jan-baranowski/atx-form-card/doc/blogpost/img/1 (3).png

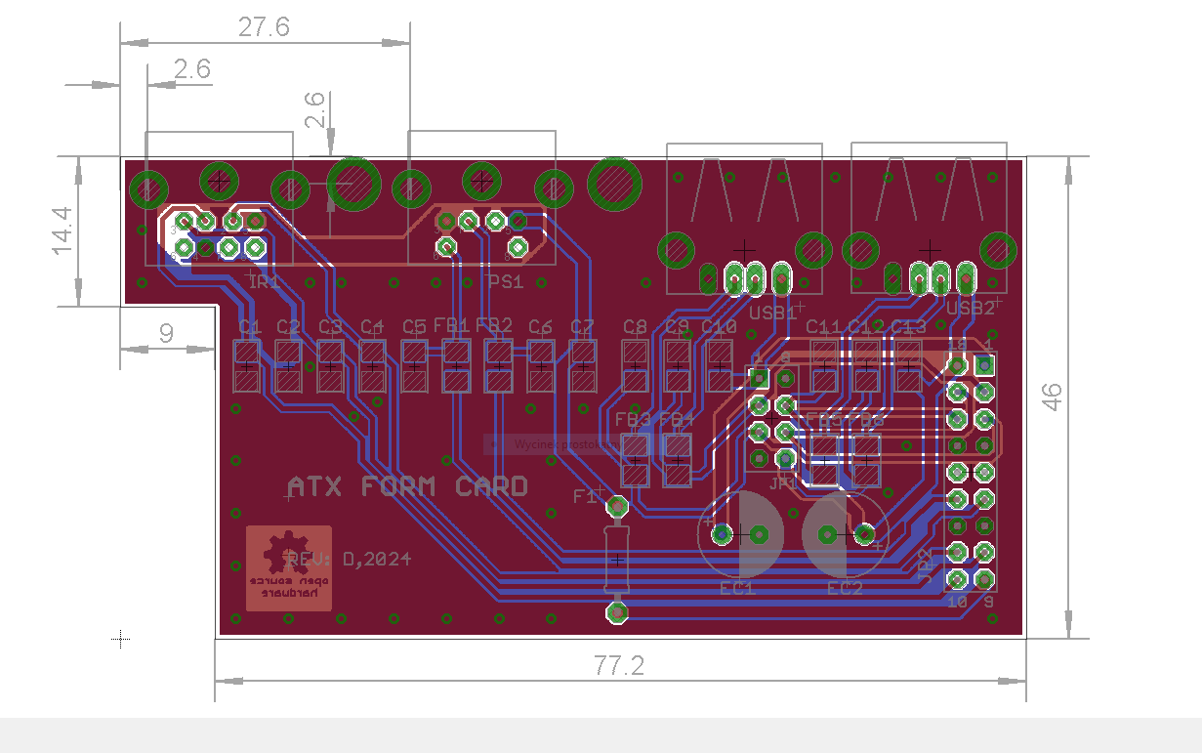
doc/blogpost/img/1 (3).png
