jan-baranowski/atx-form-card/doc/blogpost/img/1.png

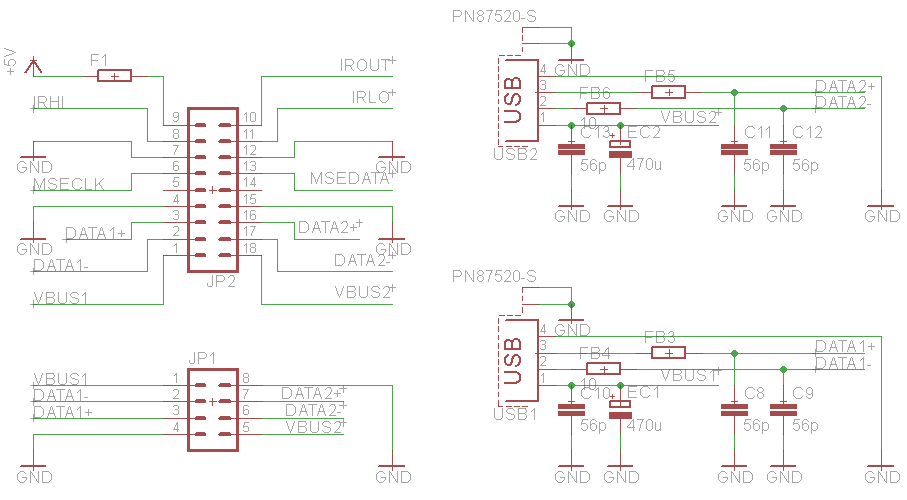
doc/blogpost/img/1.png
