jan-baranowski/atx-form-card/doc/blogpost/img/2 (2).PNG

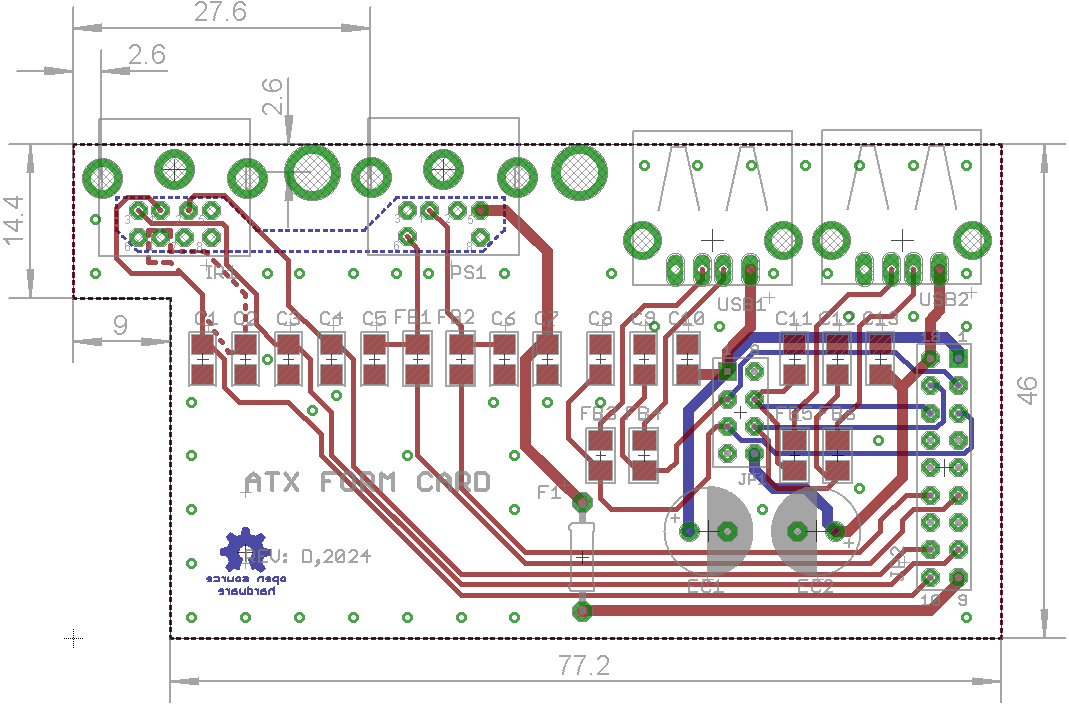
doc/blogpost/img/2 (2).PNG
