jan-baranowski/atx-form-card/doc/blogpost/img/2 (3).PNG

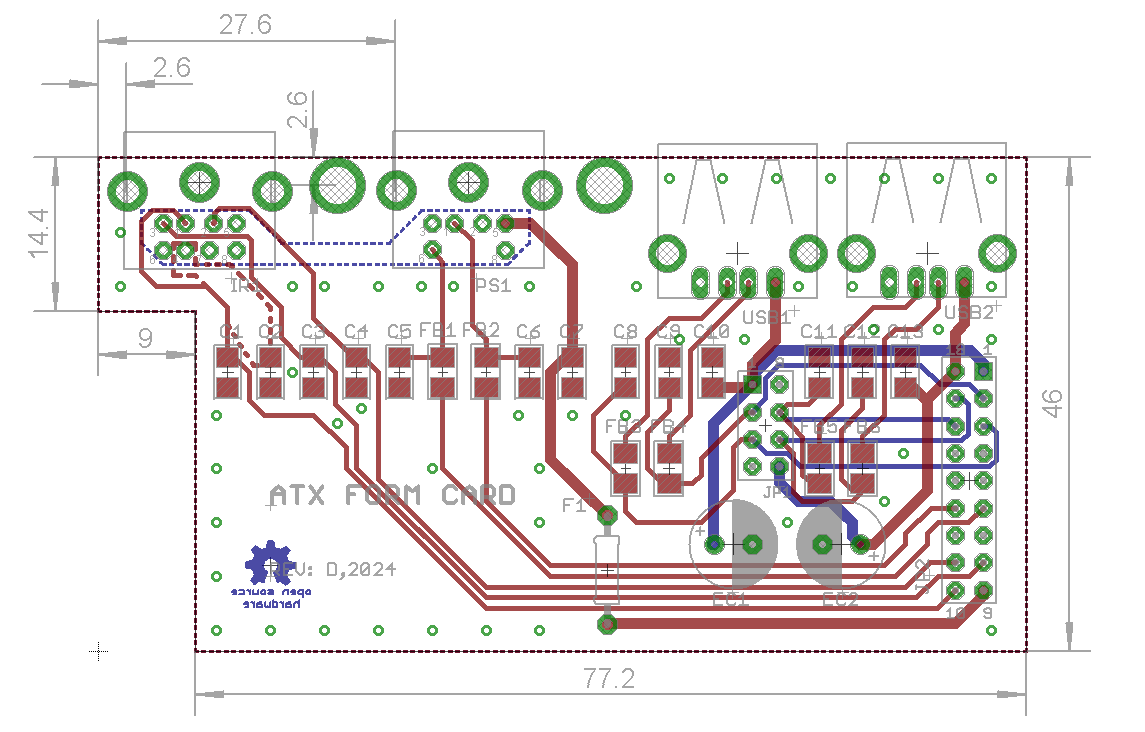
doc/blogpost/img/2 (3).PNG
