jan-baranowski/atx-form-card/doc/blogpost/img/2.png

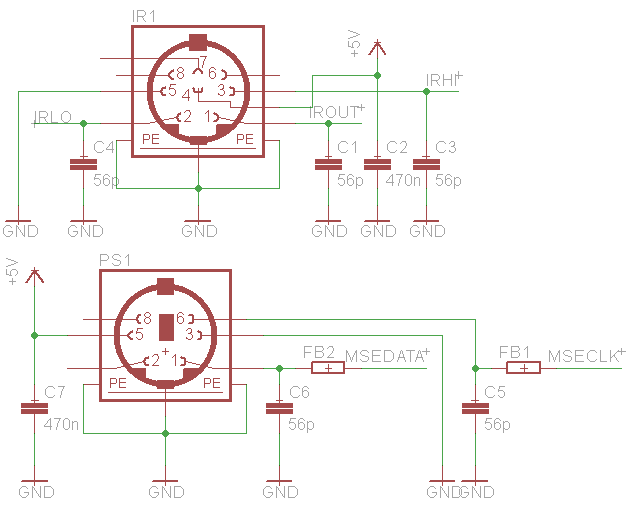
doc/blogpost/img/2.png
