jan-baranowski/atx-form-card/doc/blogpost/img/40dda3264b389b13b18e15fa20d9.jpg

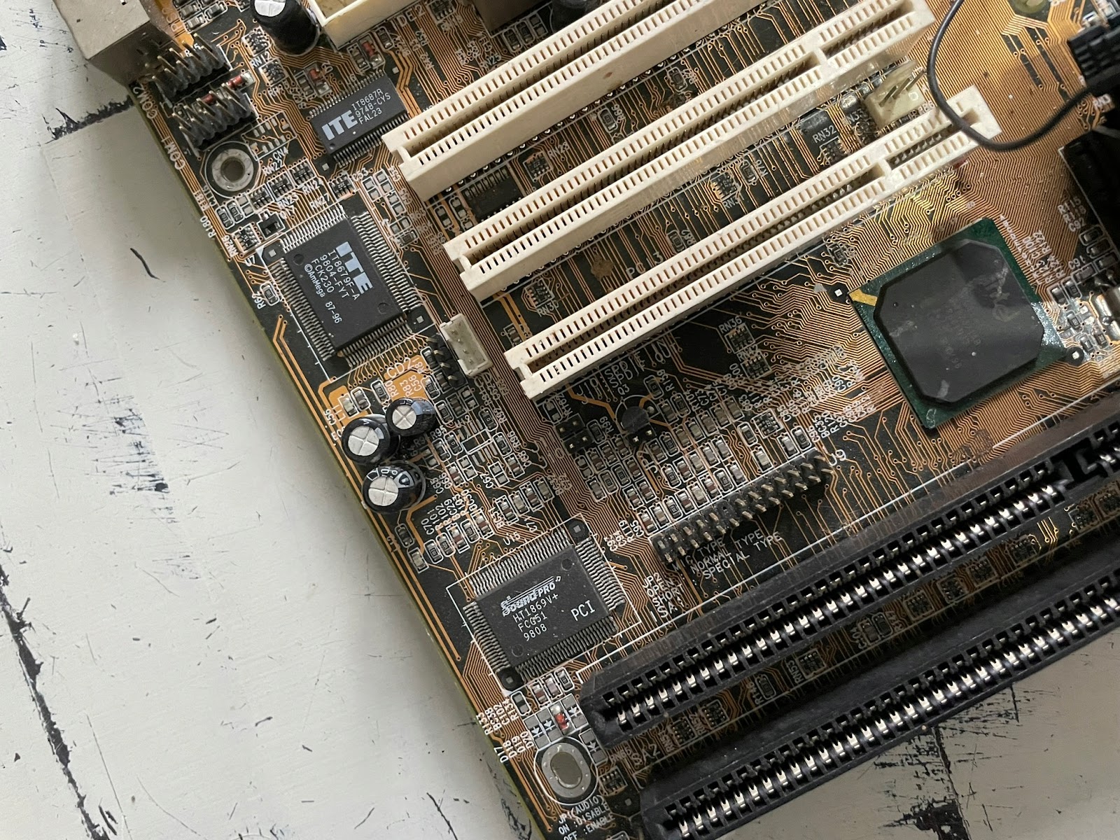
doc/blogpost/img/40dda3264b389b13b18e15fa20d9.jpg
