jan-baranowski/atx-form-card/doc/blogpost/img/2350c0874c018ecbfe8285fe1adc.jpg

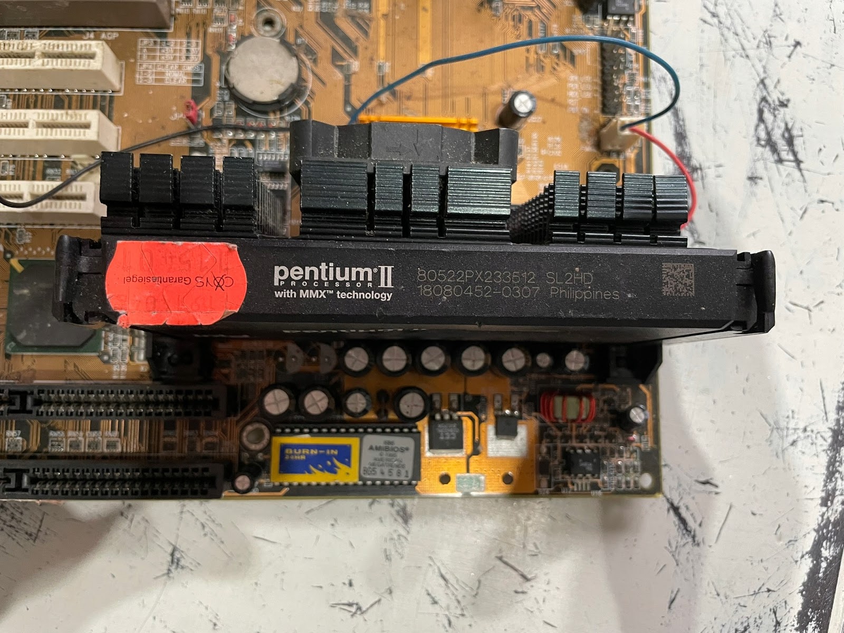
doc/blogpost/img/2350c0874c018ecbfe8285fe1adc.jpg
