jan-baranowski/atx-form-card/doc/blogpost/img/127271-002jpg_cf48e4d2-c9a6-482c-9bfb-930e1088c480_1024x1024.jpg

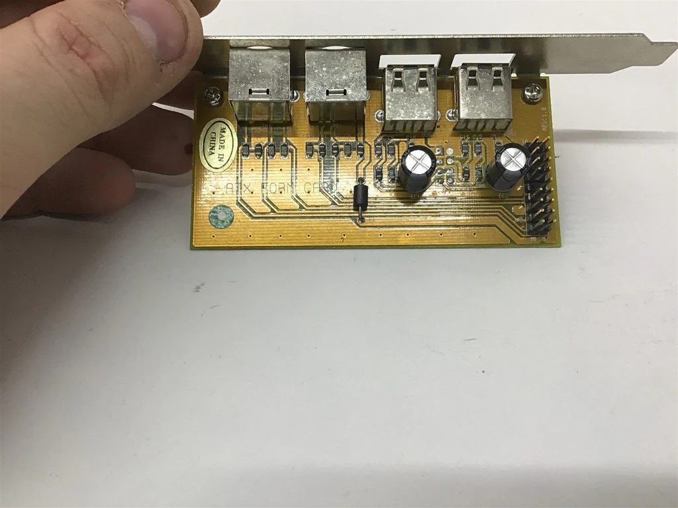
doc/blogpost/img/127271-002jpg_cf48e4d2-c9a6-482c-9bfb-930e1088c480_1024x1024.jpg
