jan-baranowski/atx-form-card/doc/blogpost/img/127271-004jpg_7a8d4e18-62b3-4fa2-aa82-eddd27a5ec42_1024x1024.jpg

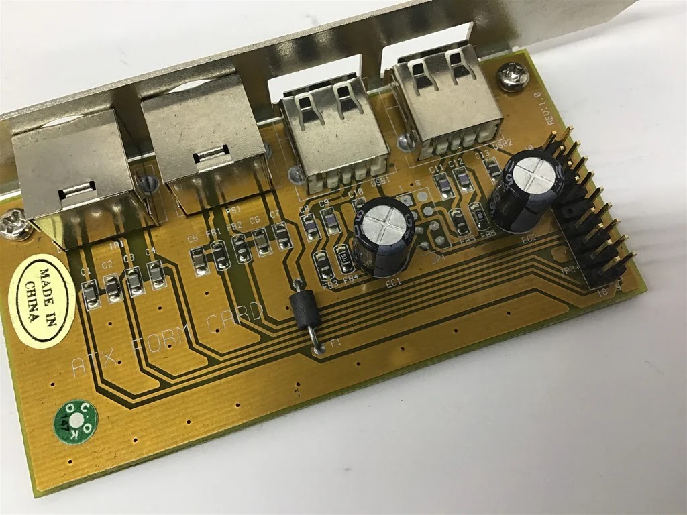
doc/blogpost/img/127271-004jpg_7a8d4e18-62b3-4fa2-aa82-eddd27a5ec42_1024x1024.jpg
