jan-baranowski/atx-form-card/doc/blogpost/img/127271-005jpg_ed1939dc-fdf4-4473-9c96-21b9dd0ac8c7_1024x1024.jpg

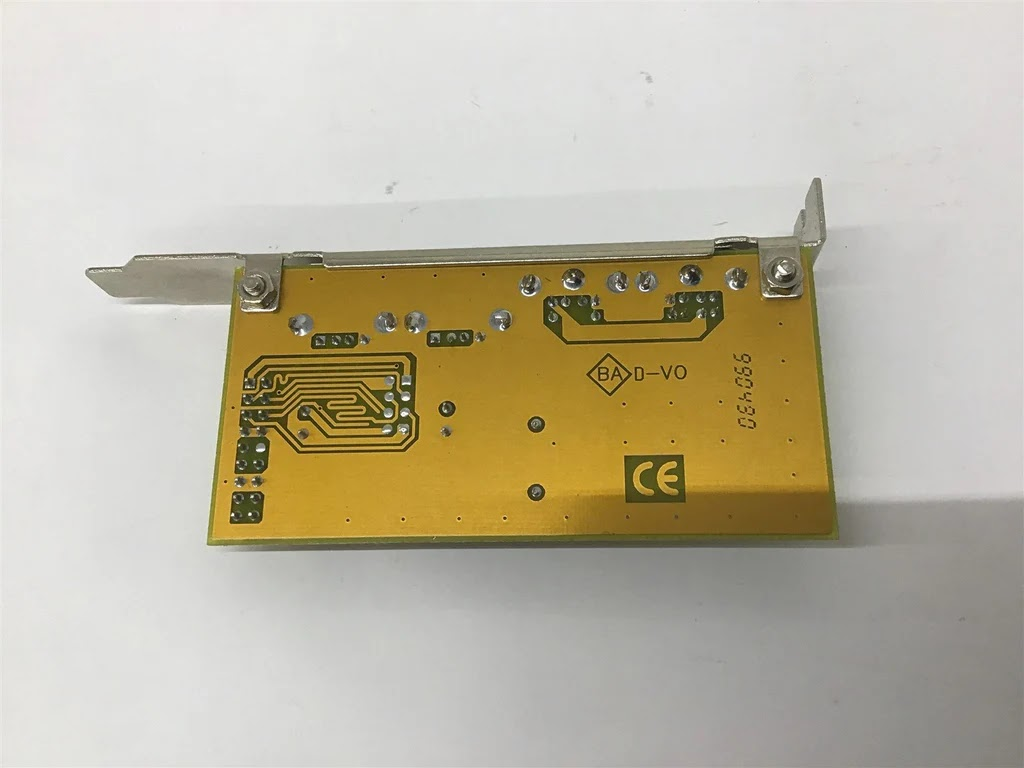
doc/blogpost/img/127271-005jpg_ed1939dc-fdf4-4473-9c96-21b9dd0ac8c7_1024x1024.jpg
