jan-baranowski/atx-form-card/doc/blogpost/img/288669ee4a689a44cc89ebede7dc.jpg

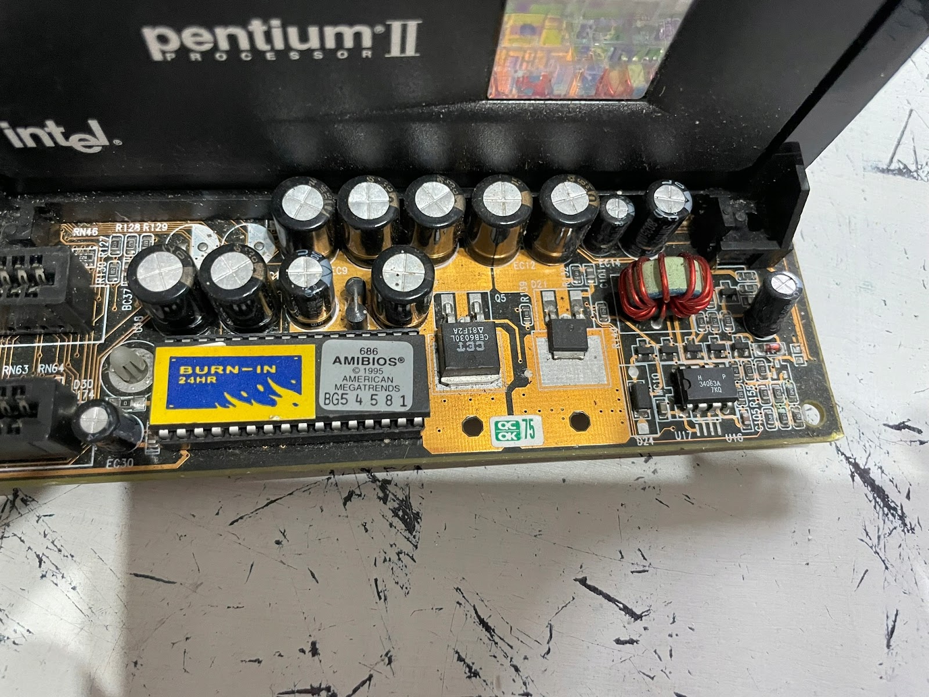
doc/blogpost/img/288669ee4a689a44cc89ebede7dc.jpg
