jan-baranowski/atx-form-card/doc/blogpost/img/atx-form-card.jpg

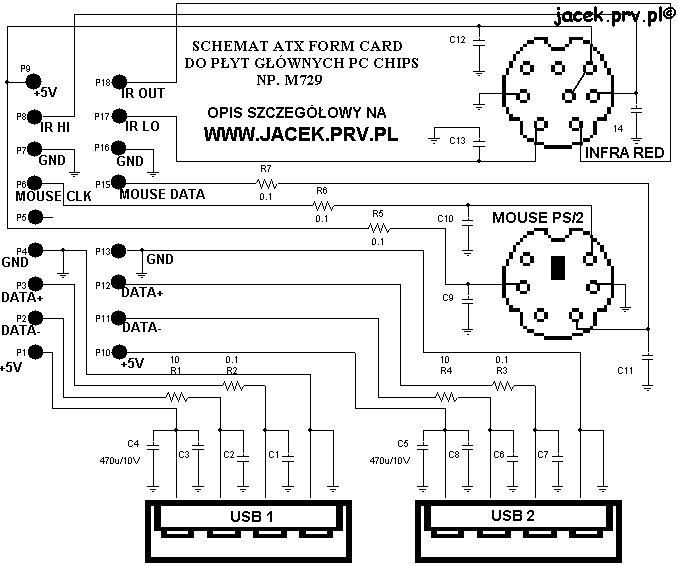
doc/blogpost/img/atx-form-card.jpg
