jan-baranowski/atx-form-card/doc/blogpost/img/bf811de64155b05a6d7ccc6c4f51.jpg

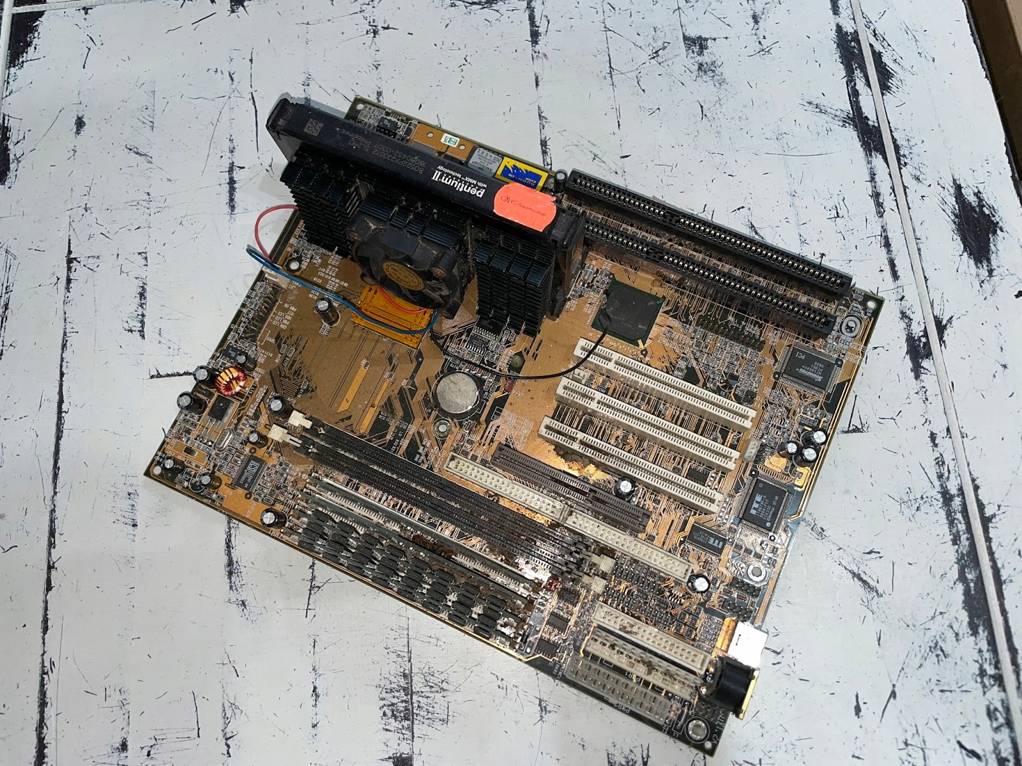
doc/blogpost/img/bf811de64155b05a6d7ccc6c4f51.jpg
