jan-baranowski/atx-form-card/doc/blogpost/img/efacdf3442a0b99acd3ed1cdcaee.jpg

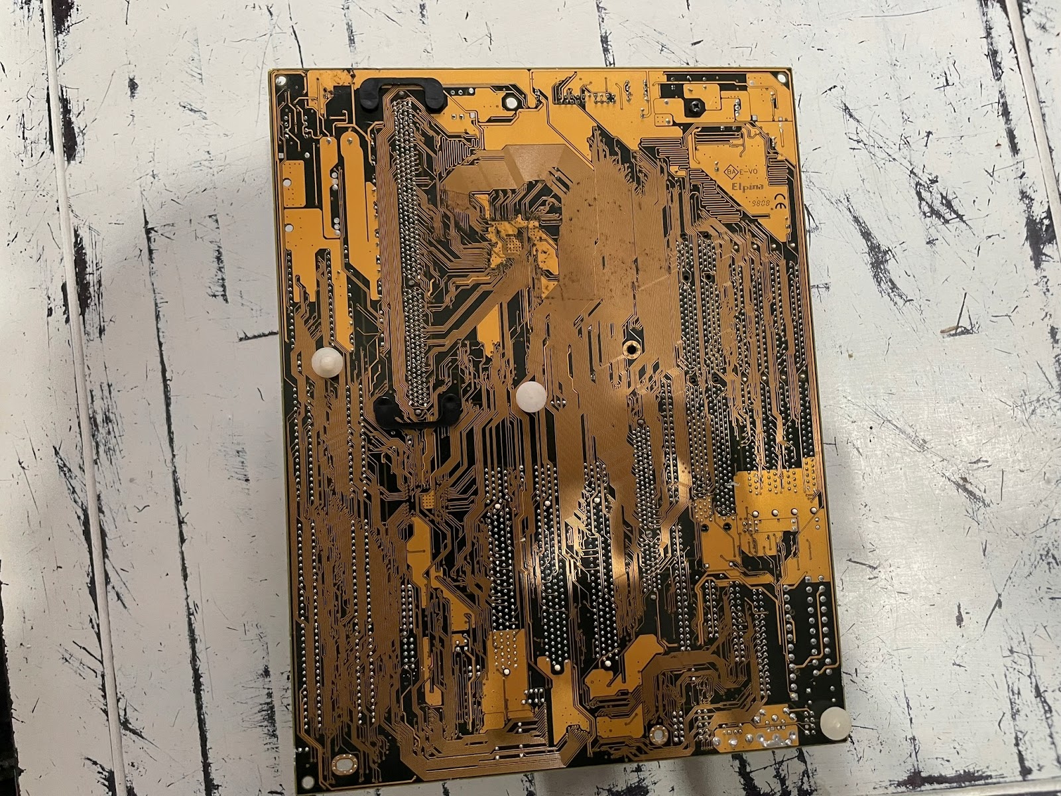
doc/blogpost/img/efacdf3442a0b99acd3ed1cdcaee.jpg
