jan-baranowski/atx-form-card/doc/blogpost/img/image;s=360x0.jpg

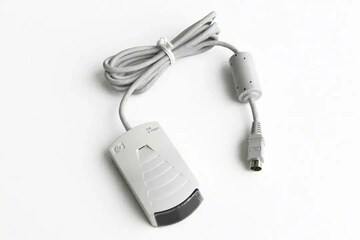
doc/blogpost/img/image;s=360x0.jpg
