jan-baranowski/atx-form-card/doc/blogpost/img/IMG_20240930_183724.jpg

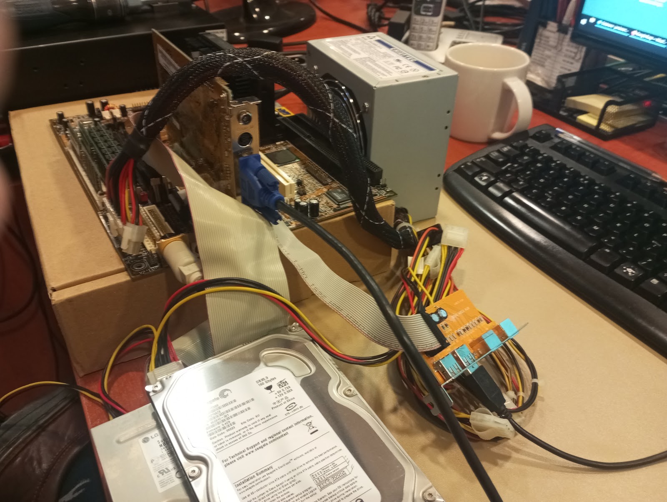
doc/blogpost/img/IMG_20240930_183724.jpg
