jan-baranowski/atx-form-card/doc/blogpost/img/IMG_20241005_171047_done_pciisa.jpg

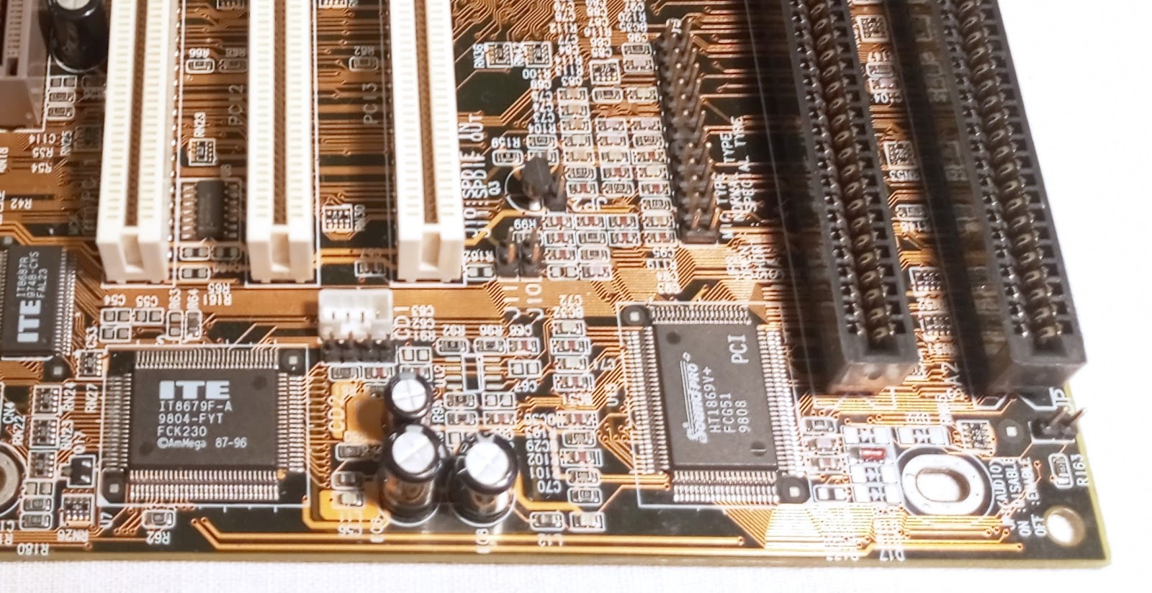
doc/blogpost/img/IMG_20241005_171047_done_pciisa.jpg
