jan-baranowski/atx-form-card/doc/blogpost/img/IMG_20241009_162338.jpg

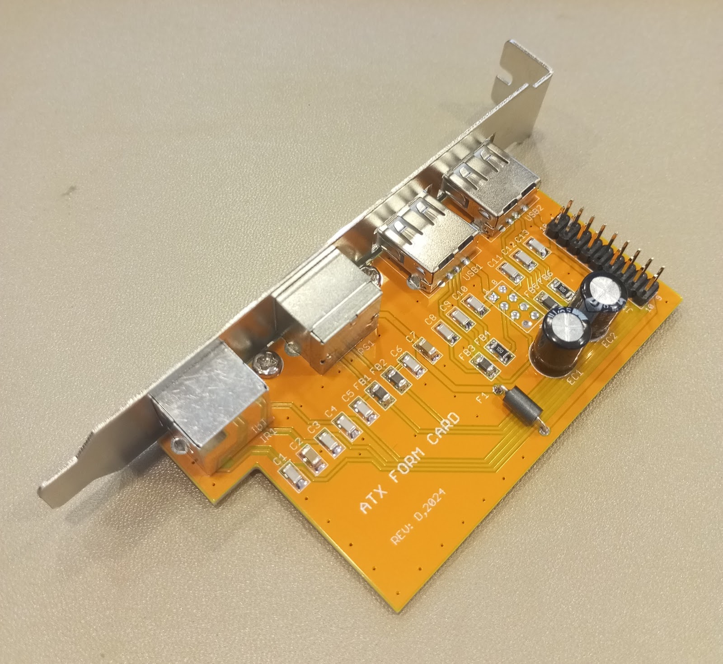
doc/blogpost/img/IMG_20241009_162338.jpg
