jan-baranowski/atx-form-card/doc/blogpost/img/IMG_20241009_162357.jpg

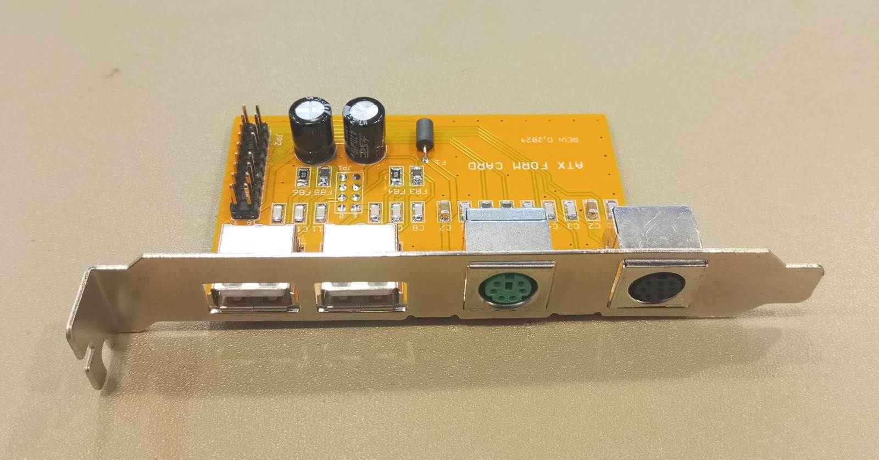
doc/blogpost/img/IMG_20241009_162357.jpg
