jan-baranowski/atx-form-card/doc/blogpost/img/IMG_20241010_175622.jpg

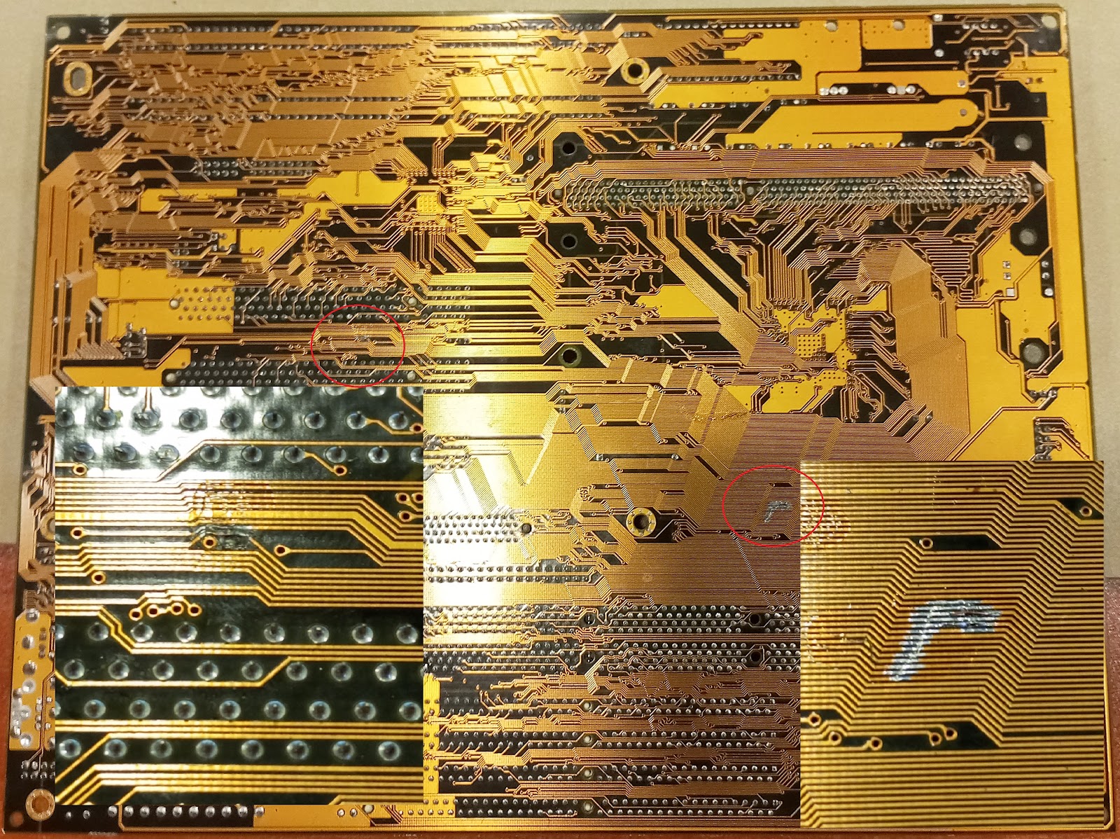
doc/blogpost/img/IMG_20241010_175622.jpg
