jan-baranowski/atx-form-card/doc/blogpost/img/IMG_20241010_180734.jpg

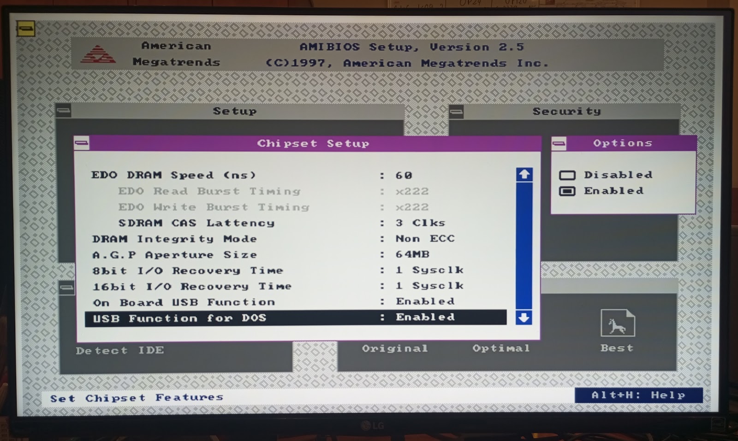
doc/blogpost/img/IMG_20241010_180734.jpg
