jan-baranowski/atx-form-card/doc/blogpost/img/OkOsC.jpg

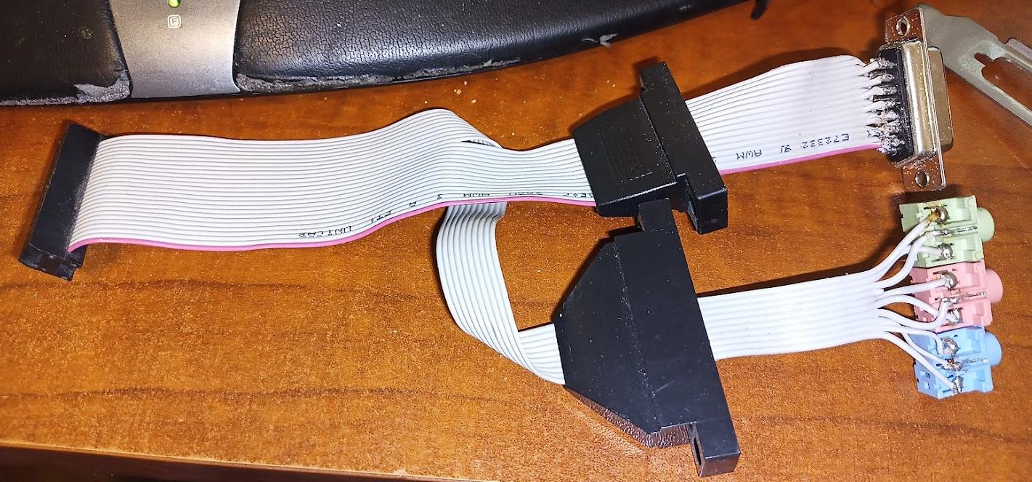
doc/blogpost/img/OkOsC.jpg
