jan-baranowski/atx-form-card/doc/blogpost/img/PC100-I-600x450.jpg

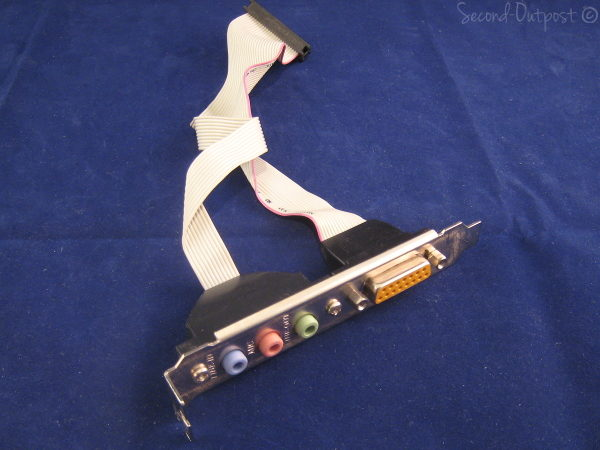
doc/blogpost/img/PC100-I-600x450.jpg
