jan-baranowski/atx-form-card/doc/blogpost/img/Przechwytywanie2.PNG

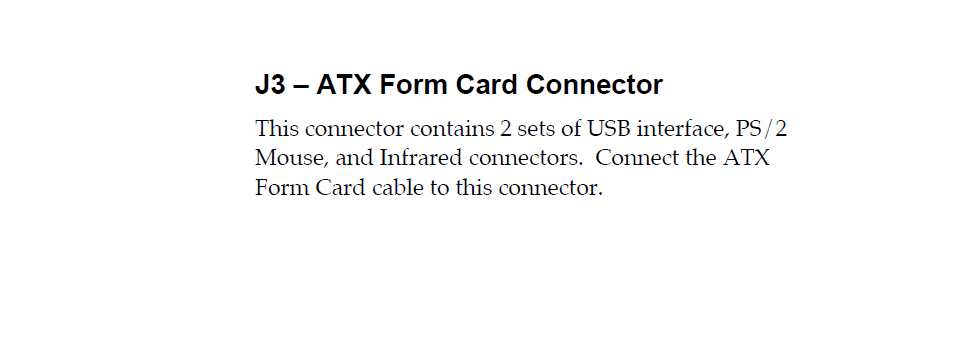
doc/blogpost/img/Przechwytywanie2.PNG
