jan-baranowski/atx-form-card/doc/blogpost/img/Przechwytywanie3.PNG

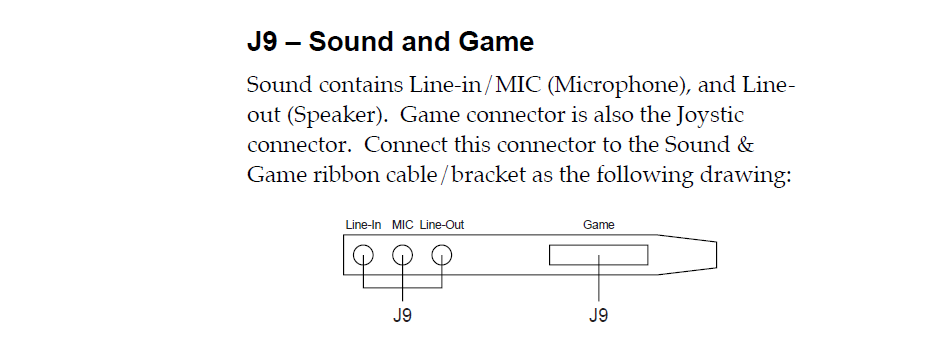
doc/blogpost/img/Przechwytywanie3.PNG
