jan-baranowski/atx-form-card/doc/blogpost/img/Przechwytywanie (2).PNG

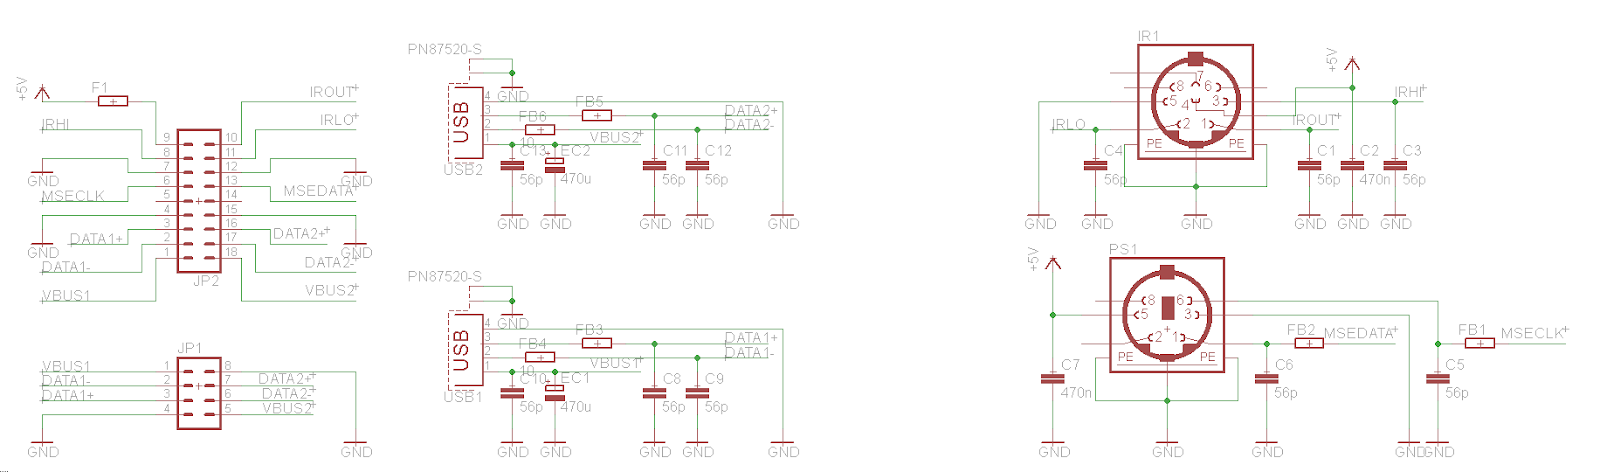
doc/blogpost/img/Przechwytywanie (2).PNG
