jan-baranowski/atx-form-card/doc/blogpost/img/Przechwytywanie.PNG

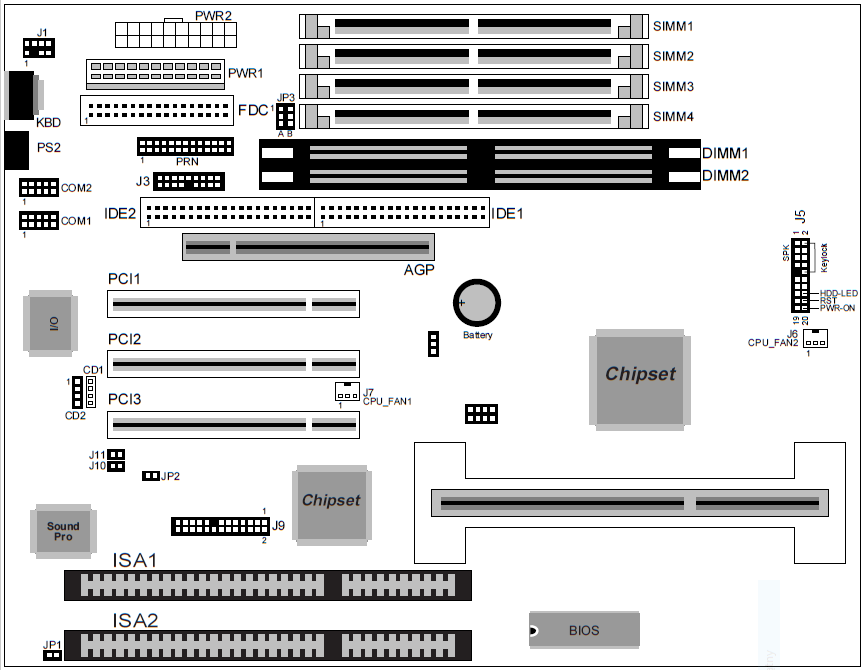
doc/blogpost/img/Przechwytywanie.PNG
