jan-baranowski/atx-form-card/doc/photo 01.jpg

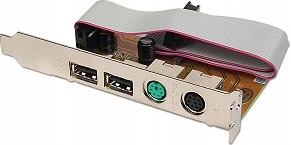
doc/photo 01.jpg
