jan-baranowski/atx-form-card/doc/photo 02.jpg

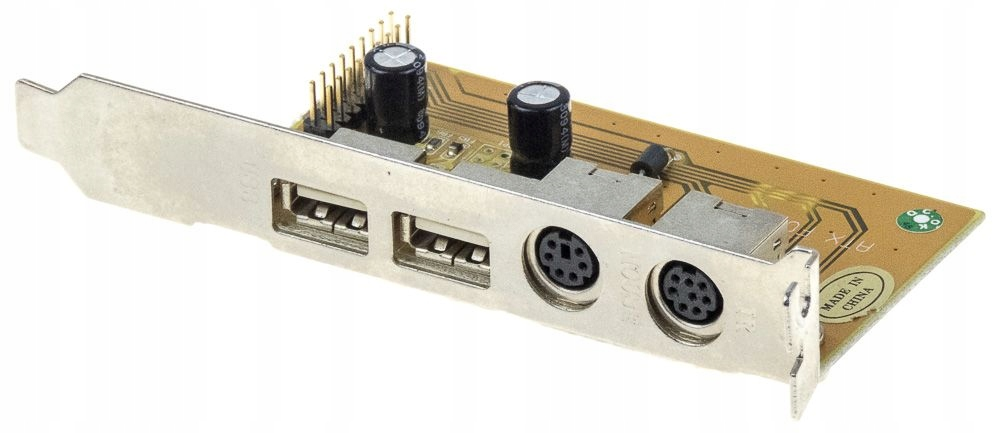
doc/photo 02.jpg
