jan-baranowski/atx-form-card/doc/photo 03.jpg

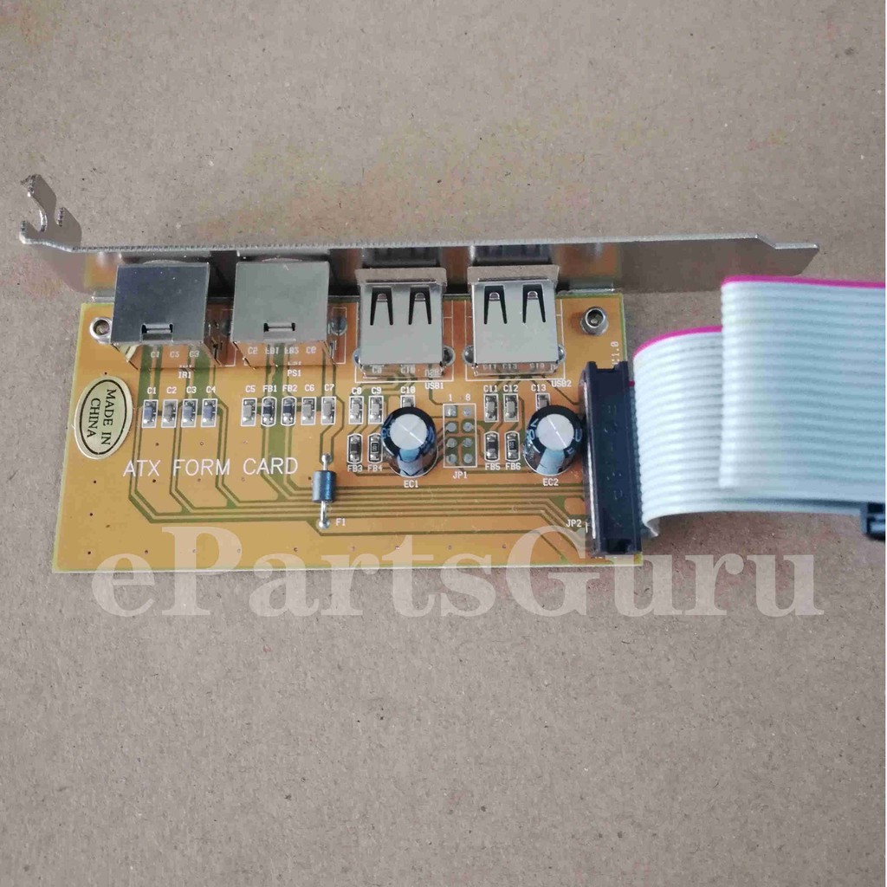
doc/photo 03.jpg
