jan-baranowski/atx-form-card/doc/photo 05.jpg

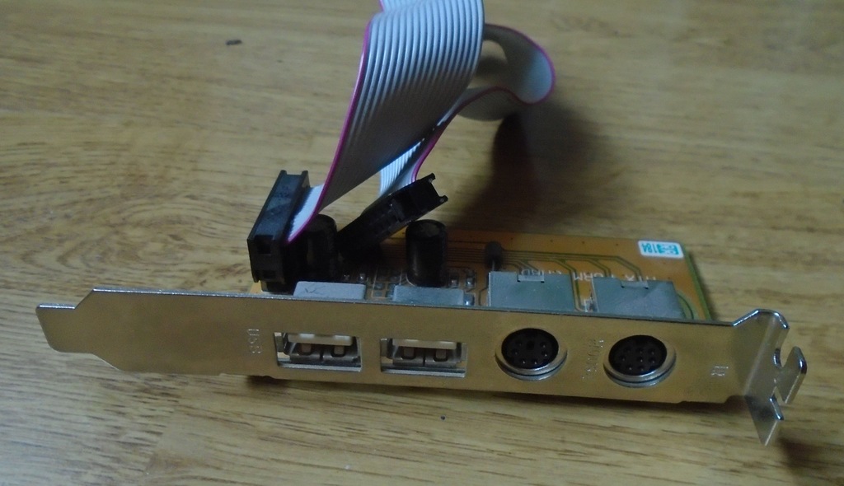
doc/photo 05.jpg
