jan-baranowski/atx-form-card/doc/photo 06.webp

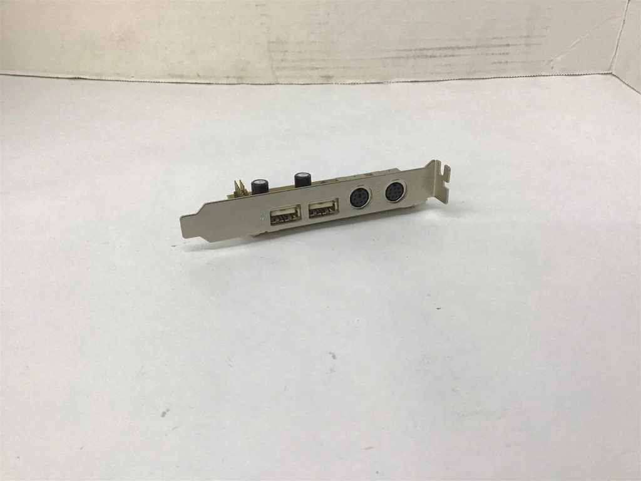
doc/photo 06.webp
