jan-baranowski/atx-form-card/doc/photo 08.webp

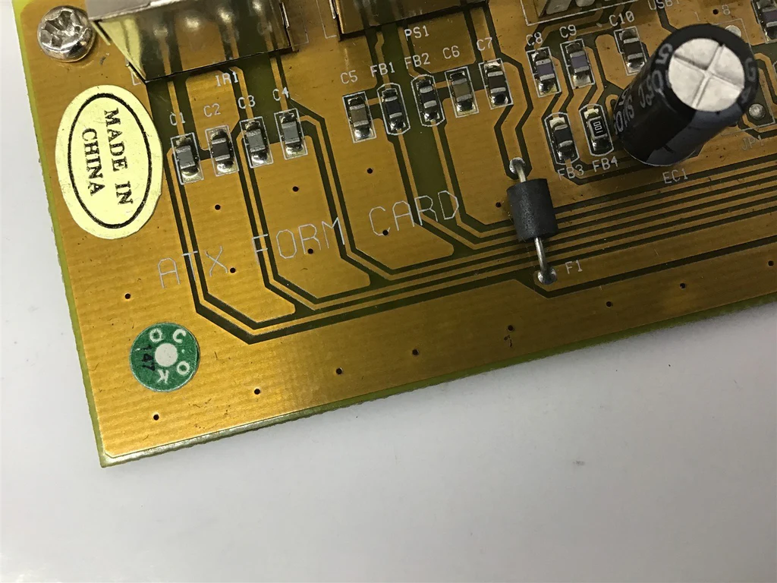
doc/photo 08.webp
