jan-baranowski/atx-form-card/doc/photo 11.webp

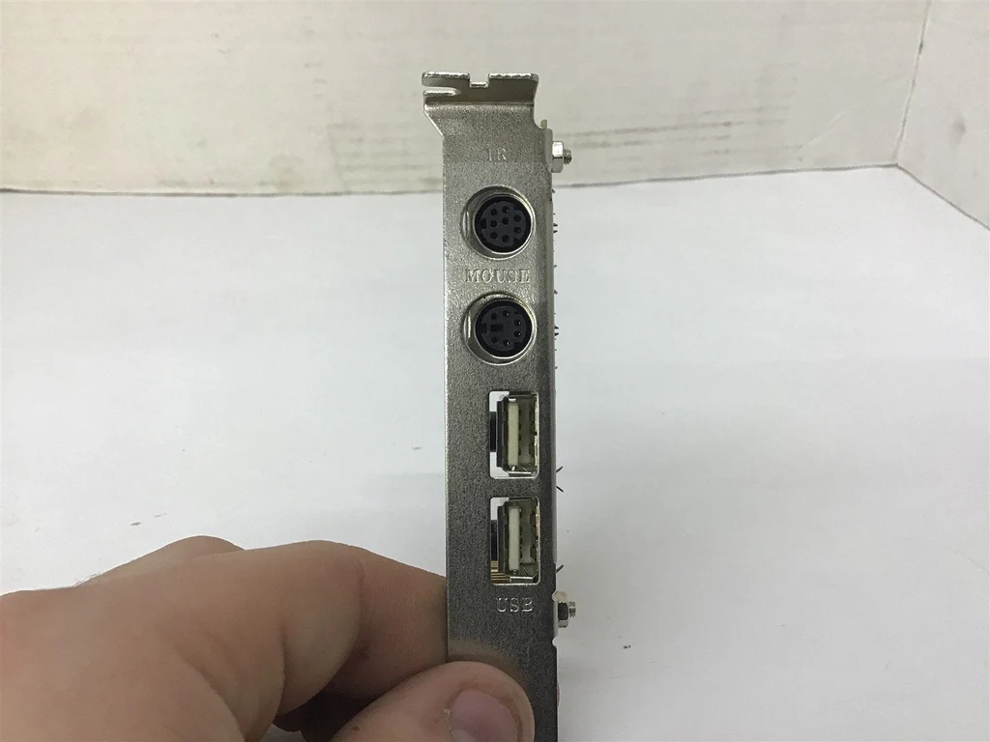
doc/photo 11.webp
