jan-baranowski/atx-form-card/doc/photo 12.jpg

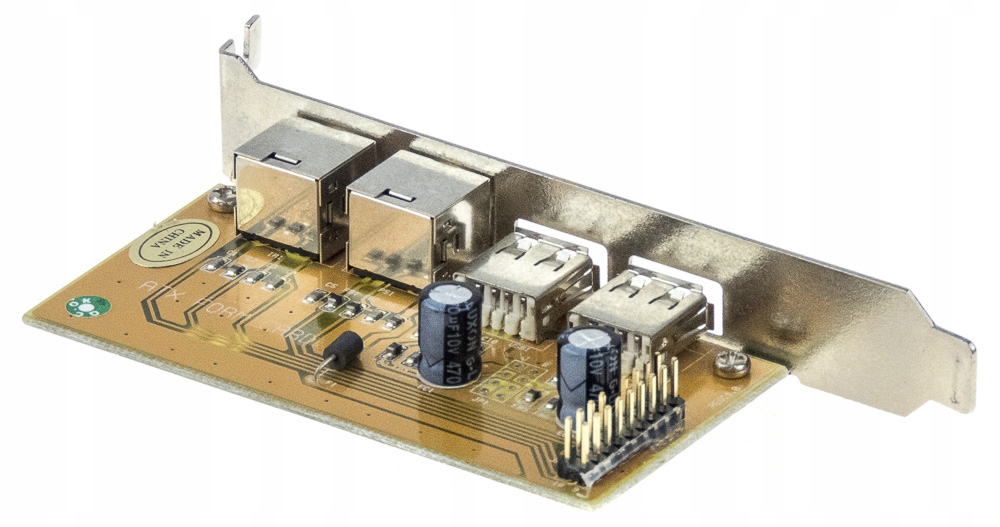
doc/photo 12.jpg
