jan-baranowski/atx-form-card/doc/photo 14.jpg

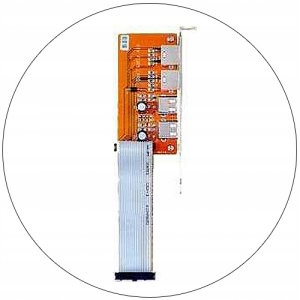
doc/photo 14.jpg
